frederikbrudy/EvalMe/images/wiring-button1.png

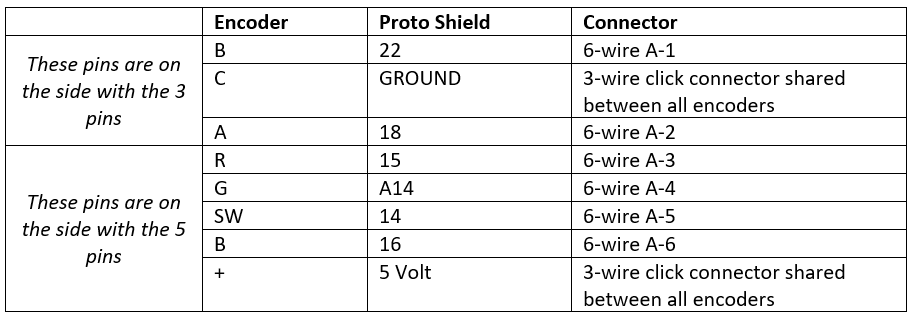
images/wiring-button1.png
